mhbbParsa/acoustic_camera/FPGA/acoustic_camera.srcs/sources_1/new/sevenseg.sv

`timescale 1ns / 1ps
//////////////////////////////////////////////////////////////////////////////////
// Company: 
// Engineer: 
// 
// Create Date: 07/11/2026 12:06:23 PM
// Design Name: 
// Module Name: sevenseg
// Project Name: 
// Target Devices: 
// Tool Versions: 
// Description: 
// 
// Dependencies: 
// 
// Revision:
// Revision 0.01 - File Created
// Additional Comments:
// 
//////////////////////////////////////////////////////////////////////////////////

module sevenseg(output logic [6:0] seg, 
                input logic [3:0] digit);

always_comb
  unique case (digit)
    4'b0000 : seg = 7'b1000000;
    4'b0001 : seg = 7'b1111001;
    4'b0010 : seg = 7'b0100100;
    4'b0011 : seg = 7'b0110000;
    4'b0100 : seg = 7'b0011001;
    4'b0101 : seg = 7'b0010010;
    4'b0110 : seg = 7'b0000010;
    4'b0111 : seg = 7'b1111000;
    4'b1000 : seg = 7'b0000000;
    4'b1001 : seg = 7'b0010000;
//    4'b1010 : seg = 7'b0001000;
//    4'b1011 : seg = 7'b0000011;
//    4'b1100 : seg = 7'b1000110;
//    4'b1101 : seg = 7'b0100001;
//    4'b1110 : seg = 7'b0000110;
//    4'b1111 : seg = 7'b0001110;
    default : seg = 7'b1111111;
  endcase
  
endmodule
